saybur/scuznet/link.c

/*
 * Copyright (C) 2019-2021 saybur
 * Copyright (C) 2021 superjer2000
 * 
 * This file is part of scuznet.
 * 
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
 * You should have received a copy of the GNU General Public License
 * along with scuznet.  If not, see <https://www.gnu.org/licenses/>.
 */

#include <stdlib.h>
#include <util/delay.h>
#include "config.h"
#include "debug.h"
#include "link.h"
#include "logic.h"
#include "enc.h"
#include "net.h"

/*
 * Maximum packet transfer length for all device types.
 * This is 14 bytes of MAC header plus up to 1500 bytes of payload.
 * See https://en.wikipedia.org/wiki/Ethernet_frame#Ethernet_II
 */
#define MAXIMUM_TRANSFER_LENGTH 1514

// the response we always send to RECEIVE DIAGNOSTIC RESULTS
#define DIAGNOSTIC_RESULTS_LENGTH 32
static const __flash uint8_t diagnostic_results[] = {
	0x43, 0x21, 0x53, 0x02, 0x40, 0x00, 0x00, 0x00,
	0x08, 0x89, 0x12, 0x04, 0x43, 0x02, 0x40, 0x00,
	0x00, 0x00, 0x08, 0x89, 0x12, 0x04, 0x43, 0x02,
	0x40, 0x00, 0x00, 0x00, 0x08, 0x89, 0x12, 0x04
};

// offsets to the MAC address information in the below data
#define MAC_ROM_OFFSET        36
#define MAC_CONFIG_OFFSET     56

// Nuvolink-compatible INQUIRY header response
static const __flash uint8_t inquiry_data_n[36] = {
	0x09, 0x00, 0x02, 0x02, 0x00, 0x00, 0x00, 0x00,
	'N', 'u', 'v', 'o', 't', 'e', 'c', 'h',
	'N', 'u', 'v', 'o', 'S', 'C', 0x00, 0x00,
	0x00, 0x00, 0x00, 0x00, 0x00, 0x00, 0x00, 0x00,
	'1', '.', '1', 'r'
};

// Daynaport-compatible INQUIRY header response
static const __flash uint8_t inquiry_data_d[255] = {
	0x03, 0x00, 0x01, 0x00, // 4 bytes
	0x1E, 0x00, 0x00, 0x00, // 4 bytes
	// Vendor ID (8 Bytes)
	'D','a','y','n','a',' ',' ',' ',
	//'D','A','Y','N','A','T','R','N',
	// Product ID (16 Bytes)
	'S','C','S','I','/','L','i','n',
	'k',' ',' ',' ',' ',' ',' ',' ',
	// Revision Number (4 Bytes)
	'1','.','4','a',
	// Firmware Version (8 Bytes)
	0x00,0x00,0x00,0x00,0x00,0x00,0x00,0x00,
	// Data
	0x00,0x00,0x00,0x00,0x00,0x00,0x00,0x00,
	0x00,0x00,0x00,0x00,0x00,0x00,0x00,0x00, //16 bytes
	0x00,0x00,0x00,0x00,0x00,0x00,0x00,0x00,
	0x00,0x00,0x00,0x00,0x00,0x00,0x00,0x00, //16 bytes
	0x00,0x00,0x00,0x00,0x00,0x00,0x00,0x00,
	0x00,0x00,0x00,0x00,0x00,0x00,0x00,0x00, //16 bytes
	0x00,0x00,0x00,0x00,0x00,0x00,0x00,0x00,
	0x00,0x00,0x00,0x00,0x00,0x00,0x00,0x00, //16 bytes
	0x00,0x00,0x00,0x00,0x00,0x00,0x00,0x00,
	0x00,0x00,0x00,0x00,0x00,0x00,0x00,0x00, //16 bytes
	0x00,0x00,0x00,0x00,0x00,0x00,0x00,0x00,
	0x00,0x00,0x00,0x00,0x00,0x00,0x00,0x00, //16 bytes
	0x00,0x00,0x00,0x00,0x00,0x00,0x00,0x00,
	0x00,0x00,0x00,0x00,0x00,0x80,0x80,0xBA, //16 bytes
	0x00,0x00,0xC0,0x00,0x00,0x00,0x00,0x00,
	0x00,0x00,0x00,0x00,0x00,0x00,0x00,0x00, //16 bytes
	0x00,0x00,0x00,0x00,0x00,0x00,0x00,0x00,
	0x00,0x00,0x00,0x00,0x00,0x00,0x00,0x00, //16 bytes
	0x00,0x00,0x00,0x00,0x00,0x00,0x00,0x00,
	0x00,0x00,0x00,0x00,0x00,0x00,0x00,0x00, //16 bytes
	0x00,0x00,0x00,0x00,0x00,0x00,0x00,0x00,
	0x00,0x00,0x00,0x81,0x00,0x00,0x00,0x00, //16 bytes
	0x00,0x00,0x00,0x00,0x00,0x00,0x00,0x00,
	0x00,0x00,0x00,0x00,0x00,0x00,0x00,0x00, //16 bytes
	0x00,0x00,0x00,0x00,0x00,0x00,0x00,0x00,
	0x00,0x00,0x00,0x00,0x00,0x00,0x00,0x00, //16 bytes
	0x00,0x00,0x00 //3 bytes
};

// the last-seen identify value
static uint8_t last_identify;

// the incremental packet counter used during packet read operations by
// the Nuvo protocol
static uint8_t rx_packet_id = 0;

// the value we use as a flag to see if we need to ask for a reselection
static uint8_t asked_for_reselection = 0;

// the dynamically configured MAC address
static uint8_t mac_dyn[6];

/*
 * Used to moderate the response to Dayna polling when emulating that device.
 * If the system responds too fast to a sent packet, the driver can become
 * confused. This value is set non-zero after a packet is sent, which prevents
 * the next poll from returning data: instead, the poll just resets the flag.
 * Polling happens fast enough under their system that this shouldn't have a
 * major impact on performance.
 */
static uint8_t dayna_wait = 0;

/*
 * ============================================================================
 *   UTILITY FUNCTIONS
 * ============================================================================
 */


static void link_send_packet(uint16_t length)
{
	if (length > MAXIMUM_TRANSFER_LENGTH)
	{
		length = MAXIMUM_TRANSFER_LENGTH;
	}

	phy_phase(PHY_PHASE_DATA_OUT);
	net_stream_write(phy_data_ask_stream, length);
	net_transmit(length);
}

/*
 * ============================================================================
 *   OPERATION HANDLERS
 * ============================================================================
 * 
 * Each of these gets called from the _main() function to perform a particular
 * task on either the device or the PHY.
 */

static void link_cmd_send_diagnostic(uint8_t* cmd)
{
	// we basically ignore this command
	uint16_t alloc = (cmd[3] << 8) + cmd[4];
	phy_phase(PHY_PHASE_DATA_OUT);
	for (uint16_t i = 0; i < alloc; i++)
	{
		phy_data_ask();
	}
	logic_status(LOGIC_STATUS_GOOD);
	logic_message_in(LOGIC_MSG_COMMAND_COMPLETE);
}

static void link_cmd_inquiry(uint8_t* cmd)
{
	/*
	 * We ignore page code and rely on allocation length only for deciding
	 * what to send, so find that first.
	 */
	uint16_t alloc = ((cmd[3] & 1) << 8) + cmd[4];
	if (debug_enabled())
	{
		debug(DEBUG_LINK_INQUIRY);
	}

	// protect against 0-length allocation
	if (alloc == 0)
	{
		// allow flow-through to completion
	}
	// otherwise switch behavior based on device type
	else if (config_enet.type == LINK_NUVO)
	{
		phy_phase(PHY_PHASE_DATA_IN);

		// do first 36 bytes of pre-programmed INQUIRY
		uint8_t limit = 36;
		if (alloc < ((uint16_t) limit)) limit = (uint8_t) alloc;
		for (uint8_t i = 0; i < limit; i++)
		{
			phy_data_offer(inquiry_data_n[i]);
		}

		// next 60 bytes
		if (alloc >= 96)
		{
			// 6 bytes of ROM MAC
			for (uint8_t i = 0; i < 6; i++)
			{
				phy_data_offer(config_enet.mac[i]);
			}
			// 14 bytes of 0x00
			for (uint8_t i = 0; i < 14; i++)
			{
				phy_data_offer(0x00);
			}
			// 6 bytes of dynamic MAC
			for (uint8_t i = 0; i < 6; i++)
			{
				phy_data_offer(mac_dyn[i]);
			}
			// 34 bytes of 0x00
			for (uint8_t i = 0; i < 34; i++)
			{
				phy_data_offer(0x00);
			}
		}

		// next 196
		if (alloc >= 292)
		{
			// bus statistics
			phy_data_offer(0x04);
			phy_data_offer(0xD2);
			for (uint8_t i = 0; i < 86; i++)
			{
				phy_data_offer(0x00);
			}
			// bus errors
			phy_data_offer(0x09);
			phy_data_offer(0x29);
			for (uint8_t i = 0; i < 58; i++)
			{
				phy_data_offer(0x00);
			}
			// network statistics
			phy_data_offer(0x0D);
			phy_data_offer(0x80);
			for (uint8_t i = 0; i < 14; i++)
			{
				phy_data_offer(0x00);
			}
			// network errors
			phy_data_offer(0x11);
			phy_data_offer(0xD7);
			for (uint8_t i = 0; i < 30; i++)
			{
				phy_data_offer(0x00);
			}
		}
	}
	else if (config_enet.type == LINK_DAYNA)
	{
		phy_phase(PHY_PHASE_DATA_IN);

		if (alloc > 255) alloc = 255;
		for (uint16_t i = 0; i < alloc; i++)
		{
			phy_data_offer(inquiry_data_d[i]);
		}
	}

	// wrap up command regardless
	if (phy_is_atn_asserted())
	{
		logic_message_out();
	}
	logic_status(LOGIC_STATUS_GOOD);
	logic_message_in(LOGIC_MSG_COMMAND_COMPLETE);
}

// TODO actually implement
static void link_cmd_change_mac(uint8_t* cmd)
{
	// fetch requested MAC address
	uint8_t alloc = 0;
	if (config_enet.type == LINK_NUVO)
	{
		alloc = cmd[4];
	}
	else if (config_enet.type == LINK_DAYNA)
	{
		alloc = 6;
	}
	if (alloc > 0)
	{
		phy_phase(PHY_PHASE_DATA_OUT);
		for (uint8_t i = 0; i < alloc; i++)
		{
			phy_data_ask();
		}
	}

	logic_status(LOGIC_STATUS_GOOD);
	logic_message_in(LOGIC_MSG_COMMAND_COMPLETE);
}

static void link_cmd_dayna_statistics(uint8_t* cmd)
{
	(void) cmd; // silence compiler

	phy_phase(PHY_PHASE_DATA_IN);

	// send MAC, then 3x DWORD 0x0 values
	phy_data_offer_bulk(mac_dyn, 6);
	for (uint8_t i = 0; i < 12; i++)
	{
		phy_data_offer(0x00);
	}

	if (phy_is_atn_asserted())
	{
		logic_message_out();
	}
	logic_status(LOGIC_STATUS_GOOD);
	logic_message_in(LOGIC_MSG_COMMAND_COMPLETE);
}

static void link_cmd_nuvo_filter(uint8_t* cmd)
{
	uint8_t data[8] = {0}; // init to 0x00 on all
	uint8_t alloc = cmd[4];
	if (alloc > 8) alloc = 8;

	/*
	 * We get 8 bytes, which I believe are targeted at the 8390's MAR0-7
	 * registers. The only patterns I've ever seen are all zeroes with the MSB
	 * of the last byte set (for MAR7, FB63, I think), or just all zeroes. If
	 * there is a different pattern, report it to the debugger.
	 */

	uint8_t unexpected = 0;
	// get the hash bytes
	phy_phase(PHY_PHASE_DATA_OUT);
	for (uint8_t i = 0; i < alloc; i++)
	{
		data[i] = phy_data_ask();
		if (i == 7)
		{
			if (data[i] != 0x80 && data[i] != 0x00) unexpected = 1;
		}
		else
		{
			if (data[i] != 0x00) unexpected = 1;
		}
	}

	// log if something unusual was found
	if (alloc != 8 || unexpected == 1)
	{
		debug_dual(DEBUG_LINK_FILTER_UNKNOWN, alloc);
		for (uint8_t i = 0; i < 8; i++) debug(data[i]);

		// fallback to accepting all multicast
		net_set_filter(NET_FILTER_UNICAST
					| NET_FILTER_BROADCAST
					| NET_FILTER_MULTICAST);
	}
	else
	{
		debug_dual(DEBUG_LINK_FILTER, data[7]);
		uint8_t v = data[7] & 0x80;
		if (v)
		{
			// corresponds to 09:00:07:FF:FF:FF for the ENC28J60
			net_hash_filter_set(7, 0x02);
			uint8_t filter = NET_FILTER_UNICAST
					| NET_FILTER_BROADCAST
					| NET_FILTER_HASH;
			net_set_filter(filter);
		}
		else
		{
			uint8_t filter = NET_FILTER_UNICAST
					| NET_FILTER_BROADCAST;
			net_set_filter(filter);
		}
	}

	logic_status(LOGIC_STATUS_GOOD);
	logic_message_in(LOGIC_MSG_COMMAND_COMPLETE);
}

static void link_cmd_dayna_filter(uint8_t* cmd)
{
	/*
	 * The DaynaPort driver sends command 0D to tell the unit what types of
	 * packets to accept. The length field of the 0D command indicates how
	 * many packet filters will be sent. The accept our MAC and broadcast
	 * seems to be generally of the form 01 00 5E 00 00 01 whereas accept
	 * AppleTalk packets will be 09 00 07 FF FF FF.
	 * 
	 * The provided addresses are fed into the hash table filter, which
	 * unfortunately accepts all packets matching the filter, not just
	 * multicast packets.
	 */

	uint16_t alloc = (cmd[3] << 8) + cmd[4];
	uint8_t filter[6];
	uint8_t fp = 0;

	net_hash_filter_reset(); // clear out old information

	phy_phase(PHY_PHASE_DATA_OUT);
	for (uint16_t i = 0; i < alloc; i++)
	{
		filter[fp++] = phy_data_ask();
		if (fp == 6)
		{
			net_hash_filter_add(filter);
			fp = 0;
		}
	}

	debug_dual(DEBUG_LINK_FILTER, alloc);
	net_set_filter(NET_FILTER_UNICAST
			| NET_FILTER_BROADCAST
			| NET_FILTER_HASH);

	logic_status(LOGIC_STATUS_GOOD);
	logic_message_in(LOGIC_MSG_COMMAND_COMPLETE);
}

static void link_cmd_nuvo_send(uint8_t* cmd)
{
	debug(DEBUG_LINK_TX_REQUESTED);

	uint16_t length = ((cmd[3] & 7) << 8) + cmd[4];
	link_send_packet(length);

	// indicate OK on TX
	logic_status(LOGIC_STATUS_GOOD);
	logic_message_in(LOGIC_MSG_COMMAND_COMPLETE);
}

static void link_cmd_dayna_send(uint8_t* cmd)
{
	debug(DEBUG_LINK_TX_REQUESTED);

	uint16_t length = ((cmd[3]) << 8) + cmd[4];

	if (cmd[5] == 0x80)
	{
		// for the XX=80, all I have ever seen is where LLLL = PPPP
		phy_phase(PHY_PHASE_DATA_OUT);
		for (uint8_t i = 0; i < 4; i++) phy_data_ask();
	}

	link_send_packet(length);
	if (! net_pending())
	{
		dayna_wait = 1;
	}

	if (cmd[5] == 0x80)
	{
		// trash trailing 4x 0x00
		phy_phase(PHY_PHASE_DATA_OUT);
		for (uint8_t i = 0; i < 4; i++) phy_data_ask();
	}

	logic_status(LOGIC_STATUS_GOOD);
	logic_message_in(LOGIC_MSG_COMMAND_COMPLETE);
}

static void link_nuvo_read_packet(void)
{
	uint8_t read_buffer[4];

	if ((net_header.stath) & 3)
	{
		// broadcast/multicast set
		read_buffer[0] = 0x21;
	}
	else
	{
		read_buffer[0] = 0x01;
	}
	read_buffer[1] = rx_packet_id++;
	read_buffer[2] = (uint8_t) (net_header.length);
	read_buffer[3] = (uint8_t) ((net_header.length) >> 8);

	phy_phase(PHY_PHASE_DATA_IN);
	phy_data_offer_bulk(read_buffer, 4);
	NETSTAT res = net_stream_read(phy_data_offer_stream_atn);
	if (res)
	{
		debug_dual(DEBUG_LINK_RX_PACKET_TRUNCATED, res);
		// as of now, do not treat this as an error
	}
}

static uint16_t link_nuvo_message_out_post_rx(void)
{
	if (! phy_is_active()) return 0;

	phy_phase(PHY_PHASE_MESSAGE_OUT);

	uint8_t message = phy_data_ask();
	if (message == LOGIC_MSG_NO_OPERATION)
	{
		// normal post-RX response, no action needed
		return 0;
	}
	else if (message == LOGIC_MSG_DISCONNECT)
	{
		/*
		 * Send a DISCONNECT of our own, hang up, and track the
		 * duration to keep from reconnecting before we're allowed
		 */
		debug(DEBUG_LINK_DISCONNECT);
		phy_phase(PHY_PHASE_MESSAGE_IN);
		phy_data_offer(LOGIC_MSG_DISCONNECT);
		phy_phase(PHY_PHASE_BUS_FREE);
		PHY_TIMER_DISCON.CTRLFSET = TC_CMD_RESTART_gc;
		PHY_TIMER_DISCON.INTFLAGS = PHY_TIMER_DISCON_OVF;
		return 0;
	}
	else if (message == 0x01)
	{
		// extended message
		uint8_t ext_len = phy_data_ask();
		if (ext_len == 3)
		{
			uint8_t ext_cmd = phy_data_ask();
			if (ext_cmd == 0xFF)
			{
				// short TX command, fetch the length
				uint16_t replay_len = phy_data_ask() << 8;
				replay_len += phy_data_ask();
				return replay_len;
			}
			else
			{
				// not a known extended message, debug and abort
				debug_dual(DEBUG_LINK_UNKNOWN_EXTENDED_MESSAGE, 0x03);
				debug(ext_cmd);
				debug(phy_data_ask());
				debug(phy_data_ask());
			}
		}
		else
		{
			// not a known extended message, debug and abort
			uint16_t ext_real_len = ext_len;
			if (ext_len == 0) ext_real_len = 256;
			debug_dual(DEBUG_LINK_UNKNOWN_EXTENDED_MESSAGE, ext_len);
			for (uint16_t i = 0; i < ext_real_len; i++)
			{
				debug(phy_data_ask());
			}
		}

		/*
		 * We go unexpectedly bus free if we didn't get the one supported
		 * extended message format.
		 */
		phy_phase(PHY_PHASE_BUS_FREE);
		return 0;
	}
	else
	{
		// message is not supported, just go bus free unexpectedly
		debug_dual(DEBUG_LINK_UNKNOWN_MESSAGE, message);
		phy_phase(PHY_PHASE_BUS_FREE);
		return 0;
	}
}

static void link_cmd_dayna_read(uint8_t* cmd)
{
	uint16_t allocation = ((cmd[3]) << 8) + cmd[4];
	if (allocation == 1)
	{
		debug(DEBUG_LINK_RX_SKIP);
		logic_status(LOGIC_STATUS_GOOD);
		logic_message_in(LOGIC_MSG_COMMAND_COMPLETE);
		return;
	}

	if (dayna_wait || ! net_pending())
	{
		// send "No Packets" message
		// debug(DEBUG_LINK_RX_NO_DATA);
		phy_phase(PHY_PHASE_DATA_IN);
		for (uint8_t i = 0; i < 6; i++)
		{
			phy_data_offer(0x00);
		}
		dayna_wait = 0;
	}
	else
	{
		uint8_t read_buffer[6];
		debug(DEBUG_LINK_RX_STARTING);

		/*
		 * Move the length bytes into the correct position. The length
		 * bytes for both Daynaport and Nuvolink seem to be the same -
		 * length of the payload excluding length and flag bytes, except
		 * little endian vs big endian.
		 */
		read_buffer[0] = (uint8_t) ((net_header.length) >> 8);
		read_buffer[1] = (uint8_t) (net_header.length);
		read_buffer[2] = 0x00;
		read_buffer[3] = 0x00;
		read_buffer[4] = 0x00;

		/*
		 * Flagging another byte as waiting does make a big difference in
		 * transfer speeds (5.4mb FILE 3:03 VS 3:35). Per the driver docs,
		 * a 0x10 means there is another packet ready to be read.
		 * Presumably this means the driver doesn't just wait for it's
		 * polling interval to elapse before asking for another packet.
		 */
		if (enc_is_int_asserted())
		{
			read_buffer[5] = 0x10;
		}
		else
		{
			read_buffer[5] = 0x00;
		}

		/*
		 * Ensure data length isn't more than the amount the driver
		 * said it can read (although this always seems to be 0x05F4
		 * which is 1524 which is 1518 + the 6 driver preamble bytes)
		 * 
		 * TODO HANDLE THIS CONDITION
		 */
/*		uint16_t 
		if (net_header.length > allocation - 6)
		{
			net_header.length = allocation - 6;
		}
*/

		phy_phase(PHY_PHASE_DATA_IN);
		// send the header
		for (uint8_t i = 0; i < 6; i++)
		{
			phy_data_offer(read_buffer[i]);
		}

		/*
		 * This pause necessary for the driver to properly read the
		 * packets. It might need to have time to parse the length out
		 * before reading the rest of it. 30us - 60us seemed to work
		 * reliably on my SE/30.  The SE did not work with 40 or 60 but
		 * did with 100.  There doesn't seem to be an significant
		 * performance penalty but there is a significant increase in
		 * compatibility.
		 */
		_delay_us(100);

		// send data
		net_stream_read(phy_data_offer_stream);
	}

	// Close out transaction
	if (phy_is_atn_asserted())
	{
		logic_message_out();
	}
	logic_status(LOGIC_STATUS_GOOD);
	logic_message_in(LOGIC_MSG_COMMAND_COMPLETE);
}

/*
 * ============================================================================
 *   EXTERNAL FUNCTIONS
 * ============================================================================
 */

void link_init()
{
	if (config_enet.id < 7 && (config_enet.type == LINK_NUVO ||
			config_enet.type == LINK_DAYNA))
	{
		for (uint8_t i = 0; i < 6; i++)
		{
			mac_dyn[i] = config_enet.mac[i];
		}
		net_set_filter(NET_FILTER_UNICAST | NET_FILTER_BROADCAST);
	}
	else
	{
		config_enet.id = 255;
		config_enet.type = LINK_NONE;
	}
}

void link_check_rx(void)
{
	// only the Nuvo protocol needs this
	if (config_enet.type != LINK_NUVO) return;

	// abort if we have not hit the disconnection delay
	if (! (PHY_TIMER_DISCON.INTFLAGS & PHY_TIMER_DISCON_OVF))
	{
		return;
	}

	if (net_pending())
	{
		if (last_identify & 0x40)
		{
			if (! asked_for_reselection)
			{
				debug(DEBUG_LINK_RX_ASKING_RESEL);
				phy_reselect(config_enet.mask);
				asked_for_reselection = 1;
			}
		}
		else
		{
			// discard packet
			debug(DEBUG_LINK_RX_SKIP);
			net_skip();
		}
	}
}

uint8_t link_main(void)
{
	if (! logic_ready()) return 0;
	if (config_enet.id == 255) return 0;
	if (phy_is_continued())
	{
		// reselection is only supported on the Nuvo device
		if (config_enet.type != LINK_NUVO) return 0;

		/*
		 * Note for below: the driver appears to be picky about timing, so we
		 * insert various waits to make sure we don't get too far ahead of it.
		 */
		debug(DEBUG_LINK_RX_STARTING);
		logic_start(0, 0);

		/*
		 * We have reselected the initiator. First step is MESSAGE OUT. This
		 * will disconnect us automatically if we get the DISCONNECT message.
		 */
		//_delay_us(65);
		logic_message_out();


		// TODO: the following loop poorly handles the delay between net_end()
		// and detecting the next packet in the queue!


		/*
		 * Then we loop, sending packets to the initiator. This will continue
		 * as long as we have packets to send (or transmit), until we get
		 * disconnected. Once done, we clear our reselection flag and then
		 * disconnect ourselves.
		 */
		uint16_t txreq = 0;
		while (phy_is_active() && (net_pending() || txreq))
		{
			if (txreq)
			{
				// initiator wants to send a packet
				debug(DEBUG_LINK_SHORT_TX_START);
				link_send_packet(txreq);

				/*
				 * I've not been able to catch this behavior on the real
				 * device. The driver appears to dislike us doing anything
				 * but disconnecting at this point.
				 */
				logic_message_in(LOGIC_MSG_DISCONNECT);
				phy_phase(PHY_PHASE_BUS_FREE);
				debug(DEBUG_LINK_SHORT_TX_DONE);
			}
			else
			{
				// nothing to transmit, just send the pending packet
				debug(DEBUG_LINK_RX_PACKET_START);
				//_delay_us(150);
				link_nuvo_read_packet();
				debug(DEBUG_LINK_RX_PACKET_DONE);
				//_delay_us(100);
				txreq = link_nuvo_message_out_post_rx();
			}
		}
		asked_for_reselection = 0;
		if (phy_is_active())
		{
			//_delay_us(150);
			logic_message_in(LOGIC_MSG_DISCONNECT);
		}
		debug(DEBUG_LINK_RX_ENDING);
	}
	else
	{
		// normal selection by initiator
		logic_start(0, 1);
		uint8_t cmd[10];
		if (! logic_command(cmd)) return 1;

		uint8_t identify = logic_identify();
		if (identify != 0) last_identify = identify;

		if (config_enet.type == LINK_NUVO)
		{
			switch (cmd[0])
			{
				case 0x02: // "Reset Stats"
					// at the moment, we have no stats to reset
					logic_status(LOGIC_STATUS_GOOD);
					logic_message_in(LOGIC_MSG_COMMAND_COMPLETE);
					break;
				case 0x03: // REQUEST SENSE
					logic_request_sense(cmd);
					break;
				case 0x05: // "Send Packet"
					link_cmd_nuvo_send(cmd);
					break;
				case 0x06: // "Change MAC"
					link_cmd_change_mac(cmd);
					break;
				case 0x09: // "Set Filter"
					link_cmd_nuvo_filter(cmd);
					break;
				case 0x12: // INQUIRY
					link_cmd_inquiry(cmd);
					break;
				case 0x1C: // RECEIVE DIAGNOSTIC
					logic_data_in_pgm(diagnostic_results, DIAGNOSTIC_RESULTS_LENGTH);
					logic_status(LOGIC_STATUS_GOOD);
					logic_message_in(LOGIC_MSG_COMMAND_COMPLETE);
					break;
				case 0x1D: // SEND DIAGNOSTIC
					link_cmd_send_diagnostic(cmd);
					break;
				case 0x00: // TEST UNIT READY
				case 0x08: // GET MESSAGE(6)
				case 0x0A: // SEND MESSAGE(6)
				case 0x0C: // "Medium Sense"
					logic_status(LOGIC_STATUS_GOOD);
					logic_message_in(LOGIC_MSG_COMMAND_COMPLETE);
					break;
				default:
					logic_cmd_illegal_op(cmd[0]);
			}
		}
		else if (config_enet.type == LINK_DAYNA)
		{
			switch (cmd[0])
			{
				case 0x03: // REQUEST SENSE
					// per device description, alloc always mis-set to 0
					// and the device always responds with 9 bytes
					cmd[4] = 9;
					logic_request_sense(cmd);
					break;
				case 0x08: // GET MESSAGE(6)
					link_cmd_dayna_read(cmd);
					break;
				case 0x09: // "Retrieve Statistics"
					link_cmd_dayna_statistics(cmd);
					break;
				case 0x0A: // SEND MESSAGE(6)
					link_cmd_dayna_send(cmd);
					break;
				case 0x0C:
					if (cmd[5] == 0x40)  // "Change MAC"
					{
						link_cmd_change_mac(cmd);
					}
					else  // "Set Interface Mode"
					{
						// broadcast always on for us
						logic_status(LOGIC_STATUS_GOOD);
						logic_message_in(LOGIC_MSG_COMMAND_COMPLETE);
					}
					break;
				case 0x0D: // "Set multicast filtering (?)"
					link_cmd_dayna_filter(cmd);
					break;
				case 0x0E: // "Enable/Disable Interface"
					// leave on all the time
					logic_status(LOGIC_STATUS_GOOD);
					logic_message_in(LOGIC_MSG_COMMAND_COMPLETE);
					break;
				case 0x12: // INQUIRY
					link_cmd_inquiry(cmd);
					break;
				case 0x00: // TEST UNIT READY
					logic_status(LOGIC_STATUS_GOOD);
					logic_message_in(LOGIC_MSG_COMMAND_COMPLETE);
					break;
				default:
					logic_cmd_illegal_op(cmd[0]);
			}
		}
	}

	logic_done();
	return 1;
}
