saybur/scuznet/hw_v02.h

/*
 * Copyright (C) 2019 saybur
 * 
 * This file is part of scuznet.
 * 
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
 * You should have received a copy of the GNU General Public License
 * along with scuznet.  If not, see <https://www.gnu.org/licenses/>.
 */

#ifndef HARDWARE_H
#define HARDWARE_H

#include <avr/io.h>

/*
 * ============================================================================
 *  
 *   PIN AND PER-HARDWARE PERIPHERAL ASSIGNMENTS
 * 
 * ============================================================================
 * 
 * Use particular caution if changing anything in the following sections. Each
 * module that uses these definitions will generally assume that it is the only
 * user of assigned resources, with resource collisions likely causing
 * undefined behavior and/or possible hardware damage.
 */

/*
 * ****************************************************************************
 * 
 *   VIRTUAL PORT ASSIGNMENTS
 * 
 * ****************************************************************************
 * 
 * The VPORT assignments on this device are static, and are likely just for
 * the PHY. Make sure to update later sections if these need to change.
 */
#define DEV_VPORT0_CFG          PORTCFG_VP02MAP_PORTA_gc
#define DEV_VPORT1_CFG          PORTCFG_VP13MAP_PORTR_gc
#define DEV_VPORT2_CFG          PORTCFG_VP02MAP_PORTC_gc
#define DEV_VPORT3_CFG          PORTCFG_VP13MAP_PORTD_gc

/*
 * ****************************************************************************
 * 
 *   DEBUGGING / REPORTING
 * 
 * ****************************************************************************
 */
#define DEBUG_USART             USARTE0
#define DEBUG_PORT              PORTE
#define DEBUG_PIN_TX            PIN3_bm
#define LED_POW_PORT            PORTE
#define LED_POW_PIN             PIN1_bm
#define LED_PORT                PORTE
#define LED_PIN                 PIN2_bm

/*
 * ****************************************************************************
 * 
 *   ETHERNET CONTROLLER
 * 
 * ****************************************************************************
 * 
 * The /INT pin must be assigned to INT0 on the relevant port. No other
 * pin interrupts are allowed on this port.
 * 
 * Address offsets are from datasheet 13.16 and the peripheral memory map is
 * from 34.
 * 
 */
#define ENC_USART               USARTE1
#define ENC_USART_BAUDCTRL      0
#define ENC_PORT                PORTE
#define ENC_PORT_OUTSET_ADDR    0x0685
#define ENC_PORT_OUTCLR_ADDR    0x0686
#define ENC_PIN_CS              PIN4_bm
#define ENC_PIN_XCK             PIN5_bm
#define ENC_PIN_RX              PIN6_bm
#define ENC_PIN_TX              PIN7_bm
#define ENC_RX_PINCTRL          PORTE.PIN6CTRL

#define ENC_PORT_EXT            PORTF
#define ENC_PORT_EXT_ICTRL_ADDR 0x06A9
#define ENC_PIN_RST             PIN4_bm
#define ENC_PIN_INT             PIN5_bm
#define ENC_INT_PINCTRL         PORTF.PIN5CTRL
#define ENC_INT_ISR             PORTF_INT0_vect

#define ENC_DMA_TX_TRIG         DMA_CH_TRIGSRC_USARTE1_DRE_gc
#define ENC_DMA_RX_TRIG         DMA_CH_TRIGSRC_USARTE1_RXC_gc

/*
 * ****************************************************************************
 * 
 *   MEMORY CARD
 * 
 * ****************************************************************************
 */
#define MEM_USART               USARTF0
#define MEM_PORT                PORTF
#define MEM_PIN_CS              PIN0_bm
#define MEM_PIN_XCK             PIN1_bm
#define MEM_PIN_RX              PIN2_bm
#define MEM_PIN_TX              PIN3_bm
#define MEM_PINCTRL_RX          PORTF.PIN2CTRL
#define MEM_DMA_TX_TRIG         DMA_CH_TRIGSRC_USARTF0_DRE_gc
#define MEM_DMA_RX_TRIG         DMA_CH_TRIGSRC_USARTF0_RXC_gc

/*
 * ****************************************************************************
 * 
 *   SCSI PHY
 * 
 * ****************************************************************************
 */

/*
 * See config.h for a description of these.
 */
#define PHY_PORT_DATA_IN_REVERSED
#define PHY_PORT_DATA_IN_INVERT
#define PHY_PORT_DATA_IN_OE

/*
 * Pin and port assignments. These end up scattered across a bunch of ports
 * to get everything assigned correctly. Things can be rearranged if needed,
 * but the following needs to be placed together:
 * 
 * 1) A port must be dedicated to the data in lines.
 * 2) Another port must be dedicated to the data out lines.
 * 3) The control inputs need to be buffered through an inverting Schmitt
 *    trigger.
 * 4) The control input lines for /BSY and /SEL need to be on the same port,
 *    and that port can have no other pin interrupts associated with it.
 * 5) Bitmasks must be set for all pins, and bit positions must be set for
 *    receiving on /ACK and transmitting on /DBP, /REQ.
 */
#define PHY_PORT_DATA_IN        PORTA
#define PHY_PORT_DATA_OUT       PORTB
#define PHY_PORT_R_RST          VPORT2
#define PHY_PORT_R_BSY          VPORT2
#define PHY_PORT_R_SEL          VPORT2
#define PHY_PORT_R_ATN          VPORT2
#define PHY_PORT_R_ACK          VPORT3
#define PHY_PORT_R_DBP          VPORT2
#define PHY_PORT_T_BSY          VPORT2
#define PHY_PORT_T_SEL          VPORT2
#define PHY_PORT_T_MSG          VPORT3
#define PHY_PORT_T_CD           VPORT3
#define PHY_PORT_T_IO           VPORT3
#define PHY_PORT_T_REQ          VPORT3
#define PHY_PORT_T_DBP          VPORT2
#define PHY_PORT_DOE            VPORT1
#define PHY_PIN_R_RST           PIN6_bm
#define PHY_PIN_R_BSY           PIN4_bm
#define PHY_PIN_R_SEL           PIN3_bm
#define PHY_PIN_R_ATN           PIN5_bm
#define PHY_PIN_R_ACK           PIN0_bm
#define PHY_PIN_R_ACK_BP        PIN0_bp
#define PHY_PIN_R_DBP           PIN2_bm
#define PHY_PIN_T_BSY           PIN7_bm
#define PHY_PIN_T_SEL           PIN1_bm
#define PHY_PIN_T_MSG           PIN3_bm
#define PHY_PIN_T_CD            PIN1_bm
#define PHY_PIN_T_IO            PIN2_bm
#define PHY_PIN_T_REQ           PIN4_bm
#define PHY_PIN_T_REQ_BP        PIN4_bp
#define PHY_PIN_T_DBP           PIN0_bm
#define PHY_PIN_T_DBP_BP        PIN0_bp
#define PHY_PIN_DOE             PIN0_bm
// a few need pin configs as well
#define PHY_CFG_R_SEL           PORTC.PIN1CTRL
#define PHY_CFG_R_BSY           PORTC.PIN4CTRL
#define PHY_CFG_R_RST           PORTC.PIN6CTRL
// and event channel information
#define PHY_CHMUX_RST           EVSYS_CHMUX_PORTC_PIN6_gc
#define PHY_CHMUX_BSY           EVSYS_CHMUX_PORTC_PIN4_gc

/*
 * Interrupt information for the port containing the /BSY and /SEL in lines.
 */
#define PHY_PORT_CTRL_IN        PORTC
#define PHY_CTRL_IN_INT0_vect   PORTC_INT0_vect
#define PHY_CTRL_IN_INT1_vect   PORTC_INT1_vect

#endif /* HARDWARE_H */
