saybur/scuznet/logic.c

/*
 * Copyright (C) 2019 saybur
 * 
 * This file is part of scuznet.
 * 
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
 * You should have received a copy of the GNU General Public License
 * along with scuznet.  If not, see <https://www.gnu.org/licenses/>.
 */

#include "config.h"
#include "debug.h"
#include "init.h"
#include "logic.h"
#include "phy.h"

/*
 * Generic NO SENSE response for REQUEST SENSE when there is nothing to report.
 * 
 * This is used to prevent having to overwrite the entire sense data array
 * whenever it is reset.
 */
static const __flash uint8_t sense_data_no_sense[] = {
	0xF0, 0x00, 0x00, 0x00,
	0x00, 0x00, 0x00, 0x0A,
	0x00, 0x00, 0x00, 0x00,
	0x00, 0x00, 0x00, 0x00,
	0x00, 0x00
};

/*
 * Bad (non-zero) LUN handling respones, for REQUEST SENSE and INQUIRY.
 * 
 * The sense data has ILLEGAL REQUEST, along with LOGICAL UNIT NOT SUPPORTED.
 */
static const __flash uint8_t sense_data_illegal_lun[] = {
	0xF0, 0x00, 0x05, 0x00,
	0x00, 0x00, 0x00, 0x0A,
	0x00, 0x00, 0x00, 0x00,
	0x25, 0x00, 0x00, 0x00,
	0x00, 0x00
};
static const __flash uint8_t inquiry_data_illegal_lun[] = {
	0x7F, 0x00, 0x02, 0x02, 0x00, 0x00, 0x00, 0x00,
	' ', 'i', 'n', 'v', 'a', 'l', 'i', 'd',
	' ', 'b', 'a', 'd', ' ', 'l', 'u', 'n',
	' ', ' ', ' ', ' ', ' ', ' ', ' ', '0'
};

// REQUEST SENSE information for each managed device
typedef struct LogicData_t {
	SENSEDATA sense;
	uint32_t value;
} LogicData;
static LogicData devices[LOGIC_DEVICE_COUNT];

static uint8_t device_id;
static uint8_t last_message_in;
static uint8_t last_identify;

/*
 * ============================================================================
 * 
 *   START / STOP HANDLERS
 * 
 * ============================================================================
 */

uint8_t logic_start(uint8_t requested_device, uint8_t check_atn)
{
	if (requested_device < LOGIC_DEVICE_COUNT)
	{
		device_id = requested_device;
	}
	else
	{
		device_id = 0;
	}
	last_message_in = 0;
	last_identify = 0;

	// attention check if requested and the state is right for it
	// phy_is_active() will be checked inside the call
	if (check_atn && phy_is_atn_asserted())
	{
		return logic_message_out();
	}
	else
	{
		return 0;
	}
}

void logic_done(void)
{
	if (phy_is_active())
	{
		phy_phase(PHY_PHASE_BUS_FREE);
	}
}

/*
 * ============================================================================
 * 
 * INFORMATION FUNCTIONS
 * 
 * ============================================================================
 */

uint8_t logic_identify(void)
{
	return last_identify;
}

uint8_t logic_sense_valid(void)
{
	return devices[device_id].sense != SENSE_OK;
}

uint8_t logic_parse_data_op(uint8_t* cmd, LogicDataOp* op)
{
	if (cmd[0] == 0x28 || cmd[0] == 0x2A || cmd[0] == 0x2B)
	{
		if (cmd[1] & 1)
		{
			// RelAddr, so nope
			logic_set_sense(SENSE_INVALID_CDB_ARGUMENT, 1);
			return 0;
		}
		else
		{
			op->lba = ((uint32_t) cmd[2] << 24)
					| ((uint32_t) cmd[3] << 16)
					| ((uint32_t) cmd[4] << 8)
					| (uint32_t) cmd[5];
			op->length = (cmd[7] << 8)
					+ cmd[8];
			return 1;
		}
	}
	else if (cmd[0] == 0x08 || cmd[0] == 0x0A || cmd[0] == 0x0B)
	{
		op->lba = ((uint32_t) (cmd[1] & 0x1F) << 16)
				| ((uint32_t) cmd[2] << 8)
				| (uint32_t) cmd[3];
		if (cmd[4] == 0)
		{
			op->length = 256;
		}
		else
		{
			op->length = cmd[4];
		}
		return 1;
	}
	else
	{
		logic_set_sense(SENSE_INVALID_CDB_OPCODE, cmd[0]);
		return 0;
	}
}

/*
 * ============================================================================
 * 
 * BUS LOGICAL OPERATIONS
 * 
 * ============================================================================
 */

uint8_t logic_message_out(void)
{
	uint8_t message = 0;

	if (! phy_is_active()) return message;
	
	do
	{
		// following will do nothing if same phase
		phy_phase(PHY_PHASE_MESSAGE_OUT);

		// get the message byte
		message = phy_data_ask();
		if (message < 0x80)
		{
			/*
			 * Most of these messages are exceptional, and should not normally
			 * be encountered. Each will note on the debugging channel, and
			 * self-handle in various ways.
			 */
			if (message == LOGIC_MSG_ABORT)
			{
				// simply go bus free
				debug_dual(DEBUG_LOGIC_MESSAGE, LOGIC_MSG_ABORT);
				phy_phase(PHY_PHASE_BUS_FREE);
			}
			else if (message == LOGIC_MSG_BUS_DEVICE_RESET)
			{
				// execute a hard reset (MCU reset)
				debug_dual(DEBUG_LOGIC_MESSAGE, LOGIC_MSG_BUS_DEVICE_RESET);
				mcu_reset();
				// in the event the reset fails, go bus free anyway
				phy_phase(PHY_PHASE_BUS_FREE);
			}
			else if (message == LOGIC_MSG_DISCONNECT)
			{
				/*
				 * Send a DISCONNECT of our own, hang up, and track the
				 * duration to keep from reconnecting before we're allowed
				 */
				debug_dual(DEBUG_LOGIC_MESSAGE, LOGIC_MSG_DISCONNECT);
				phy_phase(PHY_PHASE_MESSAGE_IN);
				phy_data_offer(LOGIC_MSG_DISCONNECT);
				phy_phase(PHY_PHASE_BUS_FREE);
				PHY_TIMER_DISCON.CTRLFSET = TC_CMD_RESTART_gc;
				PHY_TIMER_DISCON.INTFLAGS = PHY_TIMER_DISCON_OVF;
			}
			else if (message == LOGIC_MSG_INIT_DETECT_ERROR)
			{
				/*
				 * We respond by disconnecting when this happens, instead of
				 * retrying.
				 */
				debug_dual(DEBUG_LOGIC_MESSAGE, LOGIC_MSG_INIT_DETECT_ERROR);
				phy_phase(PHY_PHASE_MESSAGE_IN);
				phy_data_offer(LOGIC_MSG_DISCONNECT);
				phy_phase(PHY_PHASE_BUS_FREE);
			}
			else if (message == LOGIC_MSG_PARITY_ERROR)
			{
				// resend the last message, then allow flow to continue
				debug_dual(DEBUG_LOGIC_MESSAGE, LOGIC_MSG_PARITY_ERROR);
				phy_phase(PHY_PHASE_MESSAGE_IN);
				phy_data_offer(last_message_in);
			}
			else if (message == LOGIC_MSG_REJECT)
			{
				/*
				 * We will never send a non-mandatory message except for
				 * DISCONNECT, so this seems very unlikely to ever happen.
				 * We respond by performing an unexpected disconnect.
				 */
				debug_dual(DEBUG_LOGIC_MESSAGE, LOGIC_MSG_REJECT);
				phy_phase(PHY_PHASE_BUS_FREE);
			}
			else if (message == LOGIC_MSG_NO_OPERATION)
			{
				// ignore this message completely
			}
			else
			{
				// message is not supported
				debug_dual(DEBUG_LOGIC_UNKNOWN_MESSAGE, message);
				logic_message_in(LOGIC_MSG_REJECT);
			}
		}
		else
		{
			/*
			 * This is an identity message. We need to verify that the message
			 * is sensible before we proceed, by checking if reserved bits are
			 * set or if the initiator is attempting to execute a target
			 * routine, which we don't have.
			 */
			if (message & 0x38)
			{
				logic_message_in(LOGIC_MSG_REJECT);
			}
			else if (last_identify != 0
					&& ((last_identify & 0x07) != (message & 0x07)))
			{
				// illegal to change this after received
				phy_phase(PHY_PHASE_BUS_FREE);
			}
			else
			{
				last_identify = message;
			}
		}
	}
	while (phy_is_active() && phy_is_atn_asserted());
	return message;
}

void logic_message_in(uint8_t message_in)
{
	if (! phy_is_active()) return;
	
	phy_phase(PHY_PHASE_MESSAGE_IN);
	last_message_in = message_in;
	phy_data_offer(message_in);
	if (phy_is_atn_asserted())
	{
		logic_message_out();
	}
}

uint8_t logic_command(uint8_t* command)
{
	if (! phy_is_active()) return 0;

	// switch to COMMAND and get opcode
	phy_phase(PHY_PHASE_COMMAND);
	command[0] = phy_data_ask();

	// check opcode group which defines length
	uint8_t cmd_count;
	if (command[0] < 0x20) // group 0
	{
		// group 0, 6 bytes
		cmd_count = 6;
	}
	else if (command[0] < 0x60) // group 1 or 2
	{
		cmd_count = 10;
	}
#ifdef USE_TOOLBOX
	else if (command[0] >= 0xD0 && command[0] <= 0xD2) // toolbox
	{
		cmd_count = 10;
	}
#endif
	else // not supported
	{
		cmd_count = 1;
	}

	// read command bytes
	for (uint8_t i = 1; i < cmd_count; i++)
	{
		command[i] = phy_data_ask();
	}

	// LUN handler code
	uint8_t lun = 0xFF;
	if (last_identify)
	{
		// if set, pull from IDENTIFY data
		lun = last_identify & 3;
	}
	else if (command[0] < 0x60)
	{
		// otherwise we pull from CDB
		lun = command[1] >> 5;
	}
#ifdef USE_TOOLBOX
	else if (command[0] >= 0xD0 && command[0] <= 0xD2)
	{
		lun = 0;
	}
#endif
	if (lun)
	{
		if (command[0] == 0x12) // INQUIRY
		{
			uint8_t alloc = command[4];
			if (alloc > 36)
				alloc = 36;
			logic_data_in_pgm(inquiry_data_illegal_lun, alloc);
			logic_status(LOGIC_STATUS_GOOD);
		}
		else if (command[0] == 0x03) // REQUEST SENSE
		{
			uint8_t alloc = command[4];
			if (alloc > 18)
				alloc = 18;
			logic_data_in_pgm(sense_data_illegal_lun, alloc);
			logic_status(LOGIC_STATUS_GOOD);
		}
		else
		{
			debug(DEBUG_LOGIC_BAD_LUN);
			logic_status(LOGIC_STATUS_CHECK_CONDITION);
		}
		logic_message_in(LOGIC_MSG_COMMAND_COMPLETE);
		logic_done();
		return 0;
	}

	// command op out of range handler
#ifdef USE_TOOLBOX
	if (! (command[0] < 0x60 || (command[0] >= 0xD0 && command[0] <= 0xD2)))
#else
	if (! (command[0] < 0x60))
#endif
	{
		logic_cmd_illegal_op(command[0]);
		logic_done();
		return 0;
	}

	// check control field for flag or link bits set, which we don't support
	if (cmd_count == 6 && command[5] & 3)
	{
		logic_cmd_illegal_arg(5);
	}
	else if (cmd_count == 10 && command[9] & 3)
	{
		logic_cmd_illegal_arg(9);
	}

	/*
	 * Sense data is cleared for everything except REQUEST SENSE. It has a
	 * system for clearing sense data in its own function.
	 */
	if (command[0] != 0x03)
	{
		devices[device_id].sense = SENSE_OK;
	}

	// move to MESSAGE OUT if required
	while (phy_is_atn_asserted())
	{
		logic_message_out();
	}

	return cmd_count;
}

void logic_status(uint8_t status)
{
	if (! phy_is_active()) return;

	phy_phase(PHY_PHASE_STATUS);
	phy_data_offer(status);
	if (phy_is_atn_asserted())
	{
		logic_message_out();
	}
}

uint8_t logic_data_out(uint8_t* data, uint8_t len)
{
	if (! phy_is_active()) return 0;

	phy_phase(PHY_PHASE_DATA_OUT);
	uint8_t i;
	for (i = 0; i < len; i++)
	{
		data[i] = phy_data_ask();
	}
	if (phy_is_atn_asserted())
	{
		logic_message_out();
	}
	return i;
}

void logic_data_out_dummy(uint8_t len)
{
	if (! phy_is_active()) return;

	phy_phase(PHY_PHASE_DATA_OUT);
	for (uint8_t i = 0; i < len; i++)
	{
		phy_data_ask();
	}
	if (phy_is_atn_asserted())
	{
		logic_message_out();
	}
}

void logic_data_in(const uint8_t* data, uint8_t len)
{
	if (! phy_is_active()) return;

	phy_phase(PHY_PHASE_DATA_IN);
	for (uint8_t i = 0; i < len; i++)
	{
		phy_data_offer(data[i]);
	}
	if (phy_is_atn_asserted())
	{
		logic_message_out();
	}
}

void logic_data_in_pgm(const __flash uint8_t* data, uint8_t len)
{
	if (! phy_is_active()) return;

	phy_phase(PHY_PHASE_DATA_IN);
	for (uint8_t i = 0; i < len; i++)
	{
		phy_data_offer(data[i]);
	}
	if (phy_is_atn_asserted())
	{
		logic_message_out();
	}
}

/*
 * ============================================================================
 * 
 *   SENSE KEY / ERROR REPORTING FUNCTIONS
 * 
 * ============================================================================
 */

void logic_cmd_illegal_op(uint8_t opcode)
{
	debug_dual(DEBUG_LOGIC_BAD_CMD, opcode);

	devices[device_id].sense = SENSE_INVALID_CDB_OPCODE;
	devices[device_id].value = opcode;

	// terminate rest of command
	logic_status(LOGIC_STATUS_CHECK_CONDITION);
	logic_message_in(LOGIC_MSG_COMMAND_COMPLETE);
}

void logic_cmd_illegal_arg(uint8_t position)
{
	debug(DEBUG_LOGIC_BAD_CMD_ARGS);

	devices[device_id].sense = SENSE_INVALID_CDB_ARGUMENT;
	devices[device_id].value = position;

	// terminate rest of command
	logic_status(LOGIC_STATUS_CHECK_CONDITION);
	logic_message_in(LOGIC_MSG_COMMAND_COMPLETE);
}

void logic_set_sense(SENSEDATA sense, uint32_t value)
{
	debug_dual(DEBUG_LOGIC_SET_SENSE, sense);

	devices[device_id].sense = sense;
	devices[device_id].value = value;
}

/*
 * ============================================================================
 * 
 *   COMMON OPERATION HANDLERS
 * 
 * ============================================================================
 */

void logic_request_sense(uint8_t* cmd)
{
	uint8_t alloc = cmd[4];
	if (alloc > 18)
		alloc = 18;

	// handle the most common cases we have pre-baked data for
	if (devices[device_id].sense == SENSE_OK)
	{
		logic_data_in_pgm(sense_data_no_sense, alloc);
	}
	else
	{
		// create response data skeleton
		uint8_t sense_data[18];
		for (uint8_t i = 1; i < 18; i++)
		{
			sense_data[i] = 0x00;
		}
		sense_data[0] = 0xF0;
		sense_data[7] = 0x0A;

		// adjust reponse data according to issue
		switch (devices[device_id].sense)
		{
		case SENSE_INVALID_CDB_OPCODE:
			sense_data[2] = 0x05;
			sense_data[12] = 0x20;
			break;
		case SENSE_INVALID_CDB_ARGUMENT:
			sense_data[2] = 0x05;
			sense_data[12] = 0x24;
			sense_data[15] = 0xC0;
			sense_data[17] = devices[device_id].value;
			break;
		case SENSE_INVALID_PARAMETER:
			sense_data[2] = 0x05;
			sense_data[12] = 0x26;
			sense_data[15] = 0x80;
			sense_data[16] = devices[device_id].value >> 8;
			sense_data[17] = devices[device_id].value;
		case SENSE_ILLEGAL_LBA:
			sense_data[2] = 0x05;
			sense_data[3] = devices[device_id].value >> 24;
			sense_data[4] = devices[device_id].value >> 16;
			sense_data[5] = devices[device_id].value >> 8;
			sense_data[6] = devices[device_id].value;
		case SENSE_MEDIUM_ERROR:
			sense_data[2] = 0x03;
			break;
		case SENSE_HARDWARE_ERROR:
			sense_data[2] = 0x04;
			break;
		case SENSE_BECOMING_READY:
			sense_data[2] = 0x02;
			sense_data[12] = 0x04;
			sense_data[13] = 0x01;
			break;
		default:
			// fallback to generic hardware error
			// TODO: may want to debug this one
			sense_data[2] = 0x04;
		}

		// send information
		logic_data_in(sense_data, alloc);
	}

	// we can discard the sense data now that it has been sent
	devices[device_id].sense = SENSE_OK;

	logic_status(LOGIC_STATUS_GOOD);
	logic_message_in(LOGIC_MSG_COMMAND_COMPLETE);
}

void logic_send_diagnostic(uint8_t* cmd)
{
	uint16_t pl = (cmd[3] << 8) + cmd[4];
	if (pl > 0)
	{
		phy_phase(PHY_PHASE_DATA_OUT);
		for (uint16_t i = 0; i < pl; i++)
		{
			phy_data_ask();
		}
	}

	logic_status(LOGIC_STATUS_GOOD);
	logic_message_in(LOGIC_MSG_COMMAND_COMPLETE);
}
