saybur/scuznet/net.h

/*
 * Copyright (C) 2019 saybur
 * 
 * This file is part of scuznet.
 * 
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
 * You should have received a copy of the GNU General Public License
 * along with scuznet.  If not, see <https://www.gnu.org/licenses/>.
 */

#ifndef NET_H
#define NET_H

#include <avr/io.h>

/*
 * Declares the format of the net_header struct, which is just a copy of the
 * ENC28J60 packet header. See the datasheet for what individual components
 * mean.
 * 
 * It is critical that these values not be modified by client code!
 */
typedef struct NetHeader_t {
	uint16_t next_packet;
	uint16_t length;
	uint8_t statl;
	uint8_t stath;
} NetHeader;

// if net_pending() is true, this contains the information about the packet
extern volatile NetHeader net_header;

/*
 * Options for providing to net_set_filter. For each of these, only
 * OR-filtering is used, so a packet matching *any* of these will be accepted.
 */
#define NET_FILTER_UNICAST      0x01
#define NET_FILTER_BROADCAST    0x02
#define NET_FILTER_MULTICAST    0x04
#define NET_FILTER_HASH         0x08

/*
 * Return values for the functions.
 */
typedef enum {
	NETSTAT_OK = 0,
	NETSTAT_TRUNCATED,      // a call did not transfer all available bytes
	NETSTAT_NO_DATA         // no data are available
} NETSTAT;

/*
 * Flags within the NET_STATUS GPIOR
 * 
 * NETFLAG_PKT_PENDING: set if there is a pending packet to be read
 * NETFLAG_TXBUF: switched back and forth to support TX double-buffering
 * NETFLAG_TXUSED: set once the first packet has been sent
 */
#define NETFLAG_PKT_PENDING     _BV(1)
#define NETFLAG_TXREQ           _BV(3)

/*
 * If nonzero, there is a network packet pending and the values in net_header
 * are valid.
 */
#define net_pending()       (NET_FLAGS & NETFLAG_PKT_PENDING)

/*
 * Initalizes the Ethernet controller by writing appropriate values to its
 * registers. This should be done immediately after a controller reset to
 * restore normal function. Before calling this, MCU peripherals must be
 * correctly configured (i.e. enc_init() must have been called).
 * 
 * This needs to be given the MAC address to configure as the built-in ROM
 * address, in LSB to MSB order.
 */
void net_setup(uint8_t*);

/*
 * Updates the built-in hash filter bytes. These are eight bytes maintained
 * internally, for writing to the EHT0:7 registers on the device. These are
 * only copied over when NET_FILTER_HASH is provided to the filter call.
 * See the datasheet for details about the registers. For details about the
 * calculation, refer to the PIC18F97J60 family datasheet (inexplicably,
 * details of the hash filter calculation are missing from the ENC28J60
 * datasheet).
 * 
 * The first call accepts a six-byte MAC destination address and handles all
 * the calculations internally, setting the correct matching bit in the
 * internal array. The second call manipulates one of the bytes directly,
 * replacing it with the given value. The third call wipes the internal array
 * back to zero.
 * 
 * None of these calls will change the actual device registers. For that,
 * invoke net_set_filter() and include the hash filter selection.
 */
void net_hash_filter_add(uint8_t* mac);
void net_hash_filter_set(uint8_t idx, uint8_t value);
void net_hash_filter_reset(void);

/*
 * Updates the filtering system to match packets of the given type. Provide
 * a combination of desired types, like (NET_FILTER_UNICAST | NET_FILTER_HASH).
 */
NETSTAT net_set_filter(uint8_t ftype);

/*
 * Skips past the current packet, adjusting pointers as needed.
 */
NETSTAT net_skip(void);

/*
 * Performs a read action, streaming packet data into the given function from
 * the Ethernet controller.
 * 
 * When invoked, this will start a read operation against the network packet
 * pointed to by NET_PACKET_PTR, then call the given function with the number
 * of bytes that should be read from the given USART. Once that returns, this
 * will move the read pointers past the packet.
 * 
 * The provided function should return the number of bytes that *were not*
 * sent through properly: returning zero indicates success.
 * 
 * This will return NETSTAT_OK if all bytes were sent, and NETSTAT_TRUNCATED
 * if not all bytes were sent. The pending packet will be discarded in either
 * case.
 */ 
NETSTAT net_stream_read(uint16_t (*func)(USART_t*, uint16_t));

/*
 * Performs a buffer write, streaming data from the given function into the
 * Ethernet controller's free buffer. This does not actually transmit a packet:
 * for that, see net_transmit().
 * 
 * When invoked, this will begin a write operation, write the status byte,
 * then call the provided function with the given number of bytes that need
 * to be provided into the ENC28J60 USART.
 */
NETSTAT net_stream_write(void (*func)(USART_t*, uint16_t), uint16_t length);

/*
 * Transmits the packet in the current free buffer. Should be provided with the
 * length of the data to transmit.
 */
NETSTAT net_transmit(uint16_t length);

/*
 * Checks on the status of pending transactions. This should be called
 * intermittently in between normal transmissions to prevent the TX subsystem
 * from stalling.
 */
NETSTAT net_transmit_check(void);

#endif /* NET_H */
